apistol78/rv32/code/Runtime/GPIO.h

#pragma once

#include "Common.h"

// Directions
#define GPIO_INPUT	0
#define GPIO_OUTPUT	1

// Levels
#define GPIO_LOW	0
#define GPIO_HIGH	1

void gpio_set_direction(int pin, int direction);

void gpio_set_pin(int pin, int level);
