apistol78/rv32/board/terasic_cv_gx/ip/IP_SDRAM/alt_mem_ddrx_ecc_encoder_32_syn.v

// (C) 2001-2021 Intel Corporation. All rights reserved.
// Your use of Intel Corporation's design tools, logic functions and other 
// software and tools, and its AMPP partner logic functions, and any output 
// files from any of the foregoing (including device programming or simulation 
// files), and any associated documentation or information are expressly subject 
// to the terms and conditions of the Intel Program License Subscription 
// Agreement, Intel FPGA IP License Agreement, or other applicable 
// license agreement, including, without limitation, that your use is for the 
// sole purpose of programming logic devices manufactured by Intel and sold by 
// Intel or its authorized distributors.  Please refer to the applicable 
// agreement for further details.


// megafunction wizard: %ALTECC%
// GENERATION: STANDARD
// VERSION: WM1.0
// MODULE: altecc_encoder 

// ============================================================
// File Name: alt_mem_ddrx_ecc_encoder_32.v
// Megafunction Name(s):
// 			altecc_encoder
//
// Simulation Library Files(s):
// 			
// ============================================================
// ************************************************************
// THIS IS A WIZARD-GENERATED FILE. DO NOT EDIT THIS FILE!
//
// 10.0 Internal Build 257 07/26/2010 SP 1 PN Full Version
// ************************************************************


//Copyright (C) 1991-2010 Altera Corporation
//Your use of Altera Corporation's design tools, logic functions 
//and other software and tools, and its AMPP partner logic 
//functions, and any output files from any of the foregoing 
//(including device programming or simulation files), and any 
//associated documentation or information are expressly subject 
//to the terms and conditions of the Altera Program License 
//Subscription Agreement, Altera MegaCore Function License 
//Agreement, or other applicable license agreement, including, 
//without limitation, that your use is for the sole purpose of 
//programming logic devices manufactured by Altera and sold by 
//Altera or its authorized distributors.  Please refer to the 
//applicable agreement for further details.


//altecc_encoder device_family="Stratix III" lpm_pipeline=0 width_codeword=39 width_dataword=32 data q
//VERSION_BEGIN 10.0SP1 cbx_altecc_encoder 2010:07:26:21:21:15:PN cbx_mgl 2010:07:26:21:25:47:PN  VERSION_END
// synthesis VERILOG_INPUT_VERSION VERILOG_2001
// altera message_off 10463


//synthesis_resources = 
//synopsys translate_off
`timescale 1 ps / 1 ps
//synopsys translate_on
module  alt_mem_ddrx_ecc_encoder_32_altecc_encoder #
    ( parameter
        CFG_ECC_ENC_REG = 0
    )
	( 
        clk,
        reset_n,
	    data,
	    q
    ) /* synthesis synthesis_clearbox=1 */;
    input           clk;
    input           reset_n;
	input   [31:0]  data;
	output   [38:0]  q;

	wire  [31:0]  data_wire;
	wire  [17:0]  parity_01_wire;
	wire  [9:0]  parity_02_wire;
	wire  [4:0]  parity_03_wire;
	wire  [1:0]  parity_04_wire;
	wire  [0:0]  parity_05_wire;
	wire  [5:0]  parity_06_wire;
    wire  [37:0]  parity_final;
	wire  [37:0]  parity_final_wire;
    reg   [37:0]  parity_final_reg;
	wire  [37:0]  q_wire;
    reg   [37:0]  q_reg;

	assign
		data_wire = data,
		parity_01_wire = {
                            (data_wire[30] ^ parity_01_wire[16]),
                            (data_wire[28] ^ parity_01_wire[15]),
                            (data_wire[26] ^ parity_01_wire[14]),
                            (data_wire[25] ^ parity_01_wire[13]),
                            (data_wire[23] ^ parity_01_wire[12]),
                            (data_wire[21] ^ parity_01_wire[11]),
                            (data_wire[19] ^ parity_01_wire[10]),
                            (data_wire[17] ^ parity_01_wire[9]),
                            (data_wire[15] ^ parity_01_wire[8]),
                            (data_wire[13] ^ parity_01_wire[7]),
                            (data_wire[11] ^ parity_01_wire[6]),
                            (data_wire[10] ^ parity_01_wire[5]),
                            (data_wire[8] ^ parity_01_wire[4]),
                            (data_wire[6] ^ parity_01_wire[3]),
                            (data_wire[4] ^ parity_01_wire[2]),
                            (data_wire[3] ^ parity_01_wire[1]),
                            (data_wire[1] ^ parity_01_wire[0]),
                            data_wire[0]
                         },
		parity_02_wire = {
                            (data_wire[31] ^ parity_02_wire[8]),
                            ((data_wire[27] ^ data_wire[28]) ^ parity_02_wire[7]),
                            ((data_wire[24] ^ data_wire[25]) ^ parity_02_wire[6]),
                            ((data_wire[20] ^ data_wire[21]) ^ parity_02_wire[5]),
                            ((data_wire[16] ^ data_wire[17]) ^ parity_02_wire[4]),
                            ((data_wire[12] ^ data_wire[13]) ^ parity_02_wire[3]),
                            ((data_wire[9] ^ data_wire[10]) ^ parity_02_wire[2]),
                            ((data_wire[5] ^ data_wire[6]) ^ parity_02_wire[1]),
                            ((data_wire[2] ^ data_wire[3]) ^ parity_02_wire[0]),
                            data_wire[0]
                         },
		parity_03_wire = {
                            (((data_wire[29] ^ data_wire[30]) ^ data_wire[31]) ^ parity_03_wire[3]),
                            ((((data_wire[22] ^ data_wire[23]) ^ data_wire[24]) ^ data_wire[25]) ^ parity_03_wire[2]),
                            ((((data_wire[14] ^ data_wire[15]) ^ data_wire[16]) ^ data_wire[17]) ^ parity_03_wire[1]),
                            ((((data_wire[7] ^ data_wire[8]) ^ data_wire[9]) ^ data_wire[10]) ^ parity_03_wire[0]),
                            ((data_wire[1] ^ data_wire[2]) ^ data_wire[3])
                         },
		parity_04_wire = {
                            ((((((((data_wire[18] ^ data_wire[19]) ^ data_wire[20]) ^ data_wire[21]) ^ data_wire[22]) ^ data_wire[23]) ^ data_wire[24]) ^ data_wire[25]) ^ parity_04_wire[0]),
                            ((((((data_wire[4] ^ data_wire[5]) ^ data_wire[6]) ^ data_wire[7]) ^ data_wire[8]) ^ data_wire[9]) ^ data_wire[10])
                         },
		parity_05_wire = {
                            ((((((((((((((data_wire[11] ^ data_wire[12]) ^ data_wire[13]) ^ data_wire[14]) ^ data_wire[15]) ^ data_wire[16]) ^ data_wire[17]) ^ data_wire[18]) ^ data_wire[19]) ^ data_wire[20]) ^ data_wire[21]) ^ data_wire[22]) ^ data_wire[23]) ^ data_wire[24]) ^ data_wire[25])
                         },
		parity_06_wire = {
                            (data_wire[31] ^ parity_06_wire[4]),
                            (data_wire[30] ^ parity_06_wire[3]),
                            (data_wire[29] ^ parity_06_wire[2]),
                            (data_wire[28] ^ parity_06_wire[1]),
                            (data_wire[27] ^ parity_06_wire[0]),
                            data_wire[26]
                         },
		parity_final_wire = {
                                (q_wire[37] ^ parity_final_wire[36]),
                                (q_wire[36] ^ parity_final_wire[35]),
                                (q_wire[35] ^ parity_final_wire[34]),
                                (q_wire[34] ^ parity_final_wire[33]),
                                (q_wire[33] ^ parity_final_wire[32]),
                                (q_wire[32] ^ parity_final_wire[31]),
                                (q_wire[31] ^ parity_final_wire[30]),
                                (q_wire[30] ^ parity_final_wire[29]),
                                (q_wire[29] ^ parity_final_wire[28]),
                                (q_wire[28] ^ parity_final_wire[27]),
                                (q_wire[27] ^ parity_final_wire[26]),
                                (q_wire[26] ^ parity_final_wire[25]),
                                (q_wire[25] ^ parity_final_wire[24]),
                                (q_wire[24] ^ parity_final_wire[23]),
                                (q_wire[23] ^ parity_final_wire[22]),
                                (q_wire[22] ^ parity_final_wire[21]),
                                (q_wire[21] ^ parity_final_wire[20]),
                                (q_wire[20] ^ parity_final_wire[19]),
                                (q_wire[19] ^ parity_final_wire[18]),
                                (q_wire[18] ^ parity_final_wire[17]),
                                (q_wire[17] ^ parity_final_wire[16]),
                                (q_wire[16] ^ parity_final_wire[15]),
                                (q_wire[15] ^ parity_final_wire[14]),
                                (q_wire[14] ^ parity_final_wire[13]),
                                (q_wire[13] ^ parity_final_wire[12]),
                                (q_wire[12] ^ parity_final_wire[11]),
                                (q_wire[11] ^ parity_final_wire[10]),
                                (q_wire[10] ^ parity_final_wire[9]),
                                (q_wire[9] ^ parity_final_wire[8]),
                                (q_wire[8] ^ parity_final_wire[7]),
                                (q_wire[7] ^ parity_final_wire[6]),
                                (q_wire[6] ^ parity_final_wire[5]),
                                (q_wire[5] ^ parity_final_wire[4]),
                                (q_wire[4] ^ parity_final_wire[3]),
                                (q_wire[3] ^ parity_final_wire[2]),
                                (q_wire[2] ^ parity_final_wire[1]),
                                (q_wire[1] ^ parity_final_wire[0]),
                                 q_wire[0]
                            },
        parity_final = {
                            (q_reg[37] ^ parity_final[36]),
                            (q_reg[36] ^ parity_final[35]),
                            (q_reg[35] ^ parity_final[34]),
                            (q_reg[34] ^ parity_final[33]),
                            (q_reg[33] ^ parity_final[32]),
                            (q_reg[32] ^ parity_final[31]),
                            parity_final_reg[31 : 0]
                       },
        q = {parity_final[37], q_reg},
		q_wire = {parity_06_wire[5], parity_05_wire[0], parity_04_wire[1], parity_03_wire[4], parity_02_wire[9], parity_01_wire[17], data_wire};
        
        generate
            if (CFG_ECC_ENC_REG)
            begin
                always @ (posedge clk or negedge reset_n)
                begin
                    if (!reset_n)
                    begin
                        q_reg            <= 0;
                        parity_final_reg <= 0;
                    end
                    else
                    begin
                        q_reg            <= q_wire;
                        parity_final_reg <= parity_final_wire;
                    end
                end
            end
            else
            begin
                always @ (*)
                begin
                    q_reg            = q_wire;
                    parity_final_reg = parity_final_wire;
                end
            end
        endgenerate
        
endmodule //alt_mem_ddrx_ecc_encoder_32_altecc_encoder
//VALID FILE


// synopsys translate_off
`timescale 1 ps / 1 ps
// synopsys translate_on
module alt_mem_ddrx_ecc_encoder_32 #
    ( parameter
        CFG_ECC_ENC_REG = 0
    )
    (
        clk,
        reset_n,
	    data,
	    q
    )/* synthesis synthesis_clearbox = 1 */;

    input           clk;
    input           reset_n;
	input	[31:0]  data;
	output	[38:0]  q;

	wire [38:0] sub_wire0;
	wire [38:0] q = sub_wire0[38:0];

	alt_mem_ddrx_ecc_encoder_32_altecc_encoder #
        (
            .CFG_ECC_ENC_REG (CFG_ECC_ENC_REG)
        )
    alt_mem_ddrx_ecc_encoder_32_altecc_encoder_component
        (
            .clk (clk),
            .reset_n (reset_n),
		    .data (data),
		    .q (sub_wire0)
        );

endmodule

// ============================================================
// CNX file retrieval info
// ============================================================
// Retrieval info: PRIVATE: INTENDED_DEVICE_FAMILY STRING "Stratix III"
// Retrieval info: PRIVATE: SYNTH_WRAPPER_GEN_POSTFIX STRING "1"
// Retrieval info: LIBRARY: altera_mf altera_mf.altera_mf_components.all
// Retrieval info: CONSTANT: INTENDED_DEVICE_FAMILY STRING "Stratix III"
// Retrieval info: CONSTANT: lpm_pipeline NUMERIC "0"
// Retrieval info: CONSTANT: width_codeword NUMERIC "39"
// Retrieval info: CONSTANT: width_dataword NUMERIC "32"
// Retrieval info: USED_PORT: data 0 0 32 0 INPUT NODEFVAL "data[31..0]"
// Retrieval info: USED_PORT: q 0 0 39 0 OUTPUT NODEFVAL "q[38..0]"
// Retrieval info: CONNECT: @data 0 0 32 0 data 0 0 32 0
// Retrieval info: CONNECT: q 0 0 39 0 @q 0 0 39 0
// Retrieval info: GEN_FILE: TYPE_NORMAL alt_mem_ddrx_ecc_encoder.v FALSE
// Retrieval info: GEN_FILE: TYPE_NORMAL alt_mem_ddrx_ecc_encoder.inc FALSE
// Retrieval info: GEN_FILE: TYPE_NORMAL alt_mem_ddrx_ecc_encoder.cmp FALSE
// Retrieval info: GEN_FILE: TYPE_NORMAL alt_mem_ddrx_ecc_encoder.bsf FALSE
// Retrieval info: GEN_FILE: TYPE_NORMAL alt_mem_ddrx_ecc_encoder_inst.v FALSE
// Retrieval info: GEN_FILE: TYPE_NORMAL alt_mem_ddrx_ecc_encoder_bb.v FALSE
// Retrieval info: GEN_FILE: TYPE_NORMAL alt_mem_ddrx_ecc_encoder_32.v TRUE
// Retrieval info: GEN_FILE: TYPE_NORMAL alt_mem_ddrx_ecc_encoder_32.inc FALSE
// Retrieval info: GEN_FILE: TYPE_NORMAL alt_mem_ddrx_ecc_encoder_32.cmp FALSE
// Retrieval info: GEN_FILE: TYPE_NORMAL alt_mem_ddrx_ecc_encoder_32.bsf FALSE
// Retrieval info: GEN_FILE: TYPE_NORMAL alt_mem_ddrx_ecc_encoder_32_inst.v FALSE
// Retrieval info: GEN_FILE: TYPE_NORMAL alt_mem_ddrx_ecc_encoder_32_bb.v FALSE
// Retrieval info: GEN_FILE: TYPE_NORMAL alt_mem_ddrx_ecc_encoder_32_syn.v TRUE
