apistol78/rv32/board/terasic_cv_gx/SoC.qsf

# -------------------------------------------------------------------------- #
#
# Copyright (C) 2021  Intel Corporation. All rights reserved.
# Your use of Intel Corporation's design tools, logic functions 
# and other software and tools, and any partner logic 
# functions, and any output files from any of the foregoing 
# (including device programming or simulation files), and any 
# associated documentation or information are expressly subject 
# to the terms and conditions of the Intel Program License 
# Subscription Agreement, the Intel Quartus Prime License Agreement,
# the Intel FPGA IP License Agreement, or other applicable license
# agreement, including, without limitation, that your use is for
# the sole purpose of programming logic devices manufactured by
# Intel and sold by Intel or its authorized distributors.  Please
# refer to the applicable agreement for further details, at
# https://fpgasoftware.intel.com/eula.
#
# -------------------------------------------------------------------------- #
#
# Quartus Prime
# Version 21.1.0 Build 842 10/21/2021 SJ Lite Edition
# Date created = 17:36:14  December 13, 2021
#
# -------------------------------------------------------------------------- #
#
# Notes:
#
# 1) The default values for assignments are stored in the file:
#		MyTest_assignment_defaults.qdf
#    If this file doesn't exist, see file:
#		assignment_defaults.qdf
#
# 2) Intel recommends that you do not modify this file. This
#    file is updated automatically by the Quartus Prime software
#    and any changes you make may be lost or overwritten.
#
# -------------------------------------------------------------------------- #


set_global_assignment -name FAMILY "Cyclone V"
set_global_assignment -name DEVICE 5CGXFC5C6F27C7
set_global_assignment -name TOP_LEVEL_ENTITY SoC
set_global_assignment -name ORIGINAL_QUARTUS_VERSION 12
set_global_assignment -name PROJECT_CREATION_TIME_DATE "TUE JUN  4 20:41:15 2013"
set_global_assignment -name LAST_QUARTUS_VERSION "21.1.0 Lite Edition"
set_global_assignment -name PROJECT_OUTPUT_DIRECTORY output_files
set_global_assignment -name DEVICE_FILTER_PACKAGE FBGA
set_global_assignment -name CYCLONEII_RESERVE_NCEO_AFTER_CONFIGURATION "USE AS REGULAR IO"
set_location_assignment PIN_AB22 -to ADC_CONVST
set_location_assignment PIN_AA21 -to ADC_SCK
set_location_assignment PIN_Y10 -to ADC_SDI
set_location_assignment PIN_W10 -to ADC_SDO
set_location_assignment PIN_D7 -to AUD_ADCDAT
set_location_assignment PIN_C7 -to AUD_ADCLRCK
set_location_assignment PIN_E6 -to AUD_BCLK
set_location_assignment PIN_H10 -to AUD_DACDAT
set_location_assignment PIN_G10 -to AUD_DACLRCK
set_location_assignment PIN_D6 -to AUD_XCK
set_location_assignment PIN_U12 -to CLOCK_125_p
set_location_assignment PIN_R20 -to CLOCK_50_B5B
set_location_assignment PIN_N20 -to CLOCK_50_B6A
set_location_assignment PIN_H12 -to CLOCK_50_B7A
set_location_assignment PIN_M10 -to CLOCK_50_B8A
set_location_assignment PIN_AB24 -to CPU_RESET_n
set_location_assignment PIN_AE6 -to DDR2LP_CA[0]
set_location_assignment PIN_AF6 -to DDR2LP_CA[1]
set_location_assignment PIN_AF7 -to DDR2LP_CA[2]
set_location_assignment PIN_AF8 -to DDR2LP_CA[3]
set_location_assignment PIN_U10 -to DDR2LP_CA[4]
set_location_assignment PIN_U11 -to DDR2LP_CA[5]
set_location_assignment PIN_AE9 -to DDR2LP_CA[6]
set_location_assignment PIN_AF9 -to DDR2LP_CA[7]
set_location_assignment PIN_AB12 -to DDR2LP_CA[8]
set_location_assignment PIN_AB11 -to DDR2LP_CA[9]
set_location_assignment PIN_AF14 -to DDR2LP_CKE[0]
set_location_assignment PIN_AE13 -to DDR2LP_CKE[1]
set_location_assignment PIN_P10 -to DDR2LP_CK_n
set_location_assignment PIN_N10 -to DDR2LP_CK_p
set_location_assignment PIN_R11 -to DDR2LP_CS_n[0]
set_location_assignment PIN_T11 -to DDR2LP_CS_n[1]
set_location_assignment PIN_AF11 -to DDR2LP_DM[0]
set_location_assignment PIN_AE18 -to DDR2LP_DM[1]
set_location_assignment PIN_AE20 -to DDR2LP_DM[2]
set_location_assignment PIN_AE24 -to DDR2LP_DM[3]
set_location_assignment PIN_AA14 -to DDR2LP_DQ[0]
set_location_assignment PIN_Y14 -to DDR2LP_DQ[1]
set_location_assignment PIN_AD11 -to DDR2LP_DQ[2]
set_location_assignment PIN_AD12 -to DDR2LP_DQ[3]
set_location_assignment PIN_Y13 -to DDR2LP_DQ[4]
set_location_assignment PIN_W12 -to DDR2LP_DQ[5]
set_location_assignment PIN_AD10 -to DDR2LP_DQ[6]
set_location_assignment PIN_AF12 -to DDR2LP_DQ[7]
set_location_assignment PIN_AC15 -to DDR2LP_DQ[8]
set_location_assignment PIN_AB15 -to DDR2LP_DQ[9]
set_location_assignment PIN_AC14 -to DDR2LP_DQ[10]
set_location_assignment PIN_AF13 -to DDR2LP_DQ[11]
set_location_assignment PIN_AB16 -to DDR2LP_DQ[12]
set_location_assignment PIN_AA16 -to DDR2LP_DQ[13]
set_location_assignment PIN_AE14 -to DDR2LP_DQ[14]
set_location_assignment PIN_AF18 -to DDR2LP_DQ[15]
set_location_assignment PIN_AD16 -to DDR2LP_DQ[16]
set_location_assignment PIN_AD17 -to DDR2LP_DQ[17]
set_location_assignment PIN_AC18 -to DDR2LP_DQ[18]
set_location_assignment PIN_AF19 -to DDR2LP_DQ[19]
set_location_assignment PIN_AC17 -to DDR2LP_DQ[20]
set_location_assignment PIN_AB17 -to DDR2LP_DQ[21]
set_location_assignment PIN_AF21 -to DDR2LP_DQ[22]
set_location_assignment PIN_AE21 -to DDR2LP_DQ[23]
set_location_assignment PIN_AE15 -to DDR2LP_DQ[24]
set_location_assignment PIN_AE16 -to DDR2LP_DQ[25]
set_location_assignment PIN_AC20 -to DDR2LP_DQ[26]
set_location_assignment PIN_AD21 -to DDR2LP_DQ[27]
set_location_assignment PIN_AF16 -to DDR2LP_DQ[28]
set_location_assignment PIN_AF17 -to DDR2LP_DQ[29]
set_location_assignment PIN_AD23 -to DDR2LP_DQ[30]
set_location_assignment PIN_AF23 -to DDR2LP_DQ[31]
set_location_assignment PIN_W13 -to DDR2LP_DQS_n[0]
set_location_assignment PIN_V14 -to DDR2LP_DQS_n[1]
set_location_assignment PIN_W15 -to DDR2LP_DQS_n[2]
set_location_assignment PIN_W17 -to DDR2LP_DQS_n[3]
set_location_assignment PIN_V13 -to DDR2LP_DQS_p[0]
set_location_assignment PIN_U14 -to DDR2LP_DQS_p[1]
set_location_assignment PIN_V15 -to DDR2LP_DQS_p[2]
set_location_assignment PIN_W16 -to DDR2LP_DQS_p[3]
set_location_assignment PIN_AE11 -to DDR2LP_OCT_RZQ
set_location_assignment PIN_Y25 -to HDMI_TX_CLK
set_location_assignment PIN_V23 -to HDMI_TX_D[0]
set_location_assignment PIN_AA26 -to HDMI_TX_D[1]
set_location_assignment PIN_W25 -to HDMI_TX_D[2]
set_location_assignment PIN_W26 -to HDMI_TX_D[3]
set_location_assignment PIN_V24 -to HDMI_TX_D[4]
set_location_assignment PIN_V25 -to HDMI_TX_D[5]
set_location_assignment PIN_U24 -to HDMI_TX_D[6]
set_location_assignment PIN_T23 -to HDMI_TX_D[7]
set_location_assignment PIN_T24 -to HDMI_TX_D[8]
set_location_assignment PIN_T26 -to HDMI_TX_D[9]
set_location_assignment PIN_R23 -to HDMI_TX_D[10]
set_location_assignment PIN_R25 -to HDMI_TX_D[11]
set_location_assignment PIN_P22 -to HDMI_TX_D[12]
set_location_assignment PIN_P23 -to HDMI_TX_D[13]
set_location_assignment PIN_N25 -to HDMI_TX_D[14]
set_location_assignment PIN_P26 -to HDMI_TX_D[15]
set_location_assignment PIN_P21 -to HDMI_TX_D[16]
set_location_assignment PIN_R24 -to HDMI_TX_D[17]
set_location_assignment PIN_R26 -to HDMI_TX_D[18]
set_location_assignment PIN_AB26 -to HDMI_TX_D[19]
set_location_assignment PIN_AA24 -to HDMI_TX_D[20]
set_location_assignment PIN_AB25 -to HDMI_TX_D[21]
set_location_assignment PIN_AC25 -to HDMI_TX_D[22]
set_location_assignment PIN_AD25 -to HDMI_TX_D[23]
set_location_assignment PIN_Y26 -to HDMI_TX_DE
set_location_assignment PIN_U26 -to HDMI_TX_HS
set_location_assignment PIN_T12 -to HDMI_TX_INT
set_location_assignment PIN_U25 -to HDMI_TX_VS
set_location_assignment PIN_V19 -to HEX0[0]
set_location_assignment PIN_V18 -to HEX0[1]
set_location_assignment PIN_V17 -to HEX0[2]
set_location_assignment PIN_W18 -to HEX0[3]
set_location_assignment PIN_Y20 -to HEX0[4]
set_location_assignment PIN_Y19 -to HEX0[5]
set_location_assignment PIN_Y18 -to HEX0[6]
set_location_assignment PIN_AA18 -to HEX1[0]
set_location_assignment PIN_AD26 -to HEX1[1]
set_location_assignment PIN_AB19 -to HEX1[2]
set_location_assignment PIN_AE26 -to HEX1[3]
set_location_assignment PIN_AE25 -to HEX1[4]
set_location_assignment PIN_AC19 -to HEX1[5]
set_location_assignment PIN_AF24 -to HEX1[6]
set_location_assignment PIN_N9 -to HSMC_CLKIN0
set_location_assignment PIN_G14 -to HSMC_CLKIN_n[1]
set_location_assignment PIN_K9 -to HSMC_CLKIN_n[2]
set_location_assignment PIN_G15 -to HSMC_CLKIN_p[1]
set_location_assignment PIN_L8 -to HSMC_CLKIN_p[2]
set_location_assignment PIN_A7 -to HSMC_CLKOUT0
set_location_assignment PIN_A18 -to HSMC_CLKOUT_n[1]
set_location_assignment PIN_A16 -to HSMC_CLKOUT_n[2]
set_location_assignment PIN_A19 -to HSMC_CLKOUT_p[1]
set_location_assignment PIN_A17 -to HSMC_CLKOUT_p[2]
set_location_assignment PIN_D11 -to HSMC_D[0]
set_location_assignment PIN_H14 -to HSMC_D[1]
set_location_assignment PIN_D12 -to HSMC_D[2]
set_location_assignment PIN_H13 -to HSMC_D[3]
set_location_assignment PIN_AD2 -to HSMC_GXB_RX_p[0]
set_location_assignment PIN_AB2 -to HSMC_GXB_RX_p[1]
set_location_assignment PIN_Y2 -to HSMC_GXB_RX_p[2]
set_location_assignment PIN_V2 -to HSMC_GXB_RX_p[3]
set_location_assignment PIN_AE4 -to HSMC_GXB_TX_p[0]
set_location_assignment PIN_AC4 -to HSMC_GXB_TX_p[1]
set_location_assignment PIN_AA4 -to HSMC_GXB_TX_p[2]
set_location_assignment PIN_W4 -to HSMC_GXB_TX_p[3]
set_location_assignment PIN_M12 -to HSMC_RX_n[0]
set_location_assignment PIN_L11 -to HSMC_RX_n[1]
set_location_assignment PIN_H17 -to HSMC_RX_n[2]
set_location_assignment PIN_K11 -to HSMC_RX_n[3]
set_location_assignment PIN_J16 -to HSMC_RX_n[4]
set_location_assignment PIN_J11 -to HSMC_RX_n[5]
set_location_assignment PIN_G17 -to HSMC_RX_n[6]
set_location_assignment PIN_F12 -to HSMC_RX_n[7]
set_location_assignment PIN_F18 -to HSMC_RX_n[8]
set_location_assignment PIN_E15 -to HSMC_RX_n[9]
set_location_assignment PIN_D13 -to HSMC_RX_n[10]
set_location_assignment PIN_D15 -to HSMC_RX_n[11]
set_location_assignment PIN_D16 -to HSMC_RX_n[12]
set_location_assignment PIN_D17 -to HSMC_RX_n[13]
set_location_assignment PIN_E19 -to HSMC_RX_n[14]
set_location_assignment PIN_D20 -to HSMC_RX_n[15]
set_location_assignment PIN_A24 -to HSMC_RX_n[16]
set_location_assignment PIN_N12 -to HSMC_RX_p[0]
set_location_assignment PIN_M11 -to HSMC_RX_p[1]
set_location_assignment PIN_H18 -to HSMC_RX_p[2]
set_location_assignment PIN_L12 -to HSMC_RX_p[3]
set_location_assignment PIN_H15 -to HSMC_RX_p[4]
set_location_assignment PIN_J12 -to HSMC_RX_p[5]
set_location_assignment PIN_G16 -to HSMC_RX_p[6]
set_location_assignment PIN_G12 -to HSMC_RX_p[7]
set_location_assignment PIN_E18 -to HSMC_RX_p[8]
set_location_assignment PIN_F16 -to HSMC_RX_p[9]
set_location_assignment PIN_E13 -to HSMC_RX_p[10]
set_location_assignment PIN_C14 -to HSMC_RX_p[11]
set_location_assignment PIN_E16 -to HSMC_RX_p[12]
set_location_assignment PIN_D18 -to HSMC_RX_p[13]
set_location_assignment PIN_E20 -to HSMC_RX_p[14]
set_location_assignment PIN_D21 -to HSMC_RX_p[15]
set_location_assignment PIN_B24 -to HSMC_RX_p[16]
set_location_assignment PIN_E11 -to HSMC_TX_n[0]
set_location_assignment PIN_B9 -to HSMC_TX_n[1]
set_location_assignment PIN_C10 -to HSMC_TX_n[2]
set_location_assignment PIN_B11 -to HSMC_TX_n[3]
set_location_assignment PIN_A11 -to HSMC_TX_n[4]
set_location_assignment PIN_B19 -to HSMC_TX_n[5]
set_location_assignment PIN_C15 -to HSMC_TX_n[6]
set_location_assignment PIN_A21 -to HSMC_TX_n[7]
set_location_assignment PIN_C12 -to HSMC_TX_n[8]
set_location_assignment PIN_A9 -to HSMC_TX_n[9]
set_location_assignment PIN_A13 -to HSMC_TX_n[10]
set_location_assignment PIN_C22 -to HSMC_TX_n[11]
set_location_assignment PIN_B14 -to HSMC_TX_n[12]
set_location_assignment PIN_A22 -to HSMC_TX_n[13]
set_location_assignment PIN_B17 -to HSMC_TX_n[14]
set_location_assignment PIN_C18 -to HSMC_TX_n[15]
set_location_assignment PIN_B20 -to HSMC_TX_n[16]
set_location_assignment PIN_E10 -to HSMC_TX_p[0]
set_location_assignment PIN_C9 -to HSMC_TX_p[1]
set_location_assignment PIN_D10 -to HSMC_TX_p[2]
set_location_assignment PIN_A12 -to HSMC_TX_p[3]
set_location_assignment PIN_B10 -to HSMC_TX_p[4]
set_location_assignment PIN_C20 -to HSMC_TX_p[5]
set_location_assignment PIN_B15 -to HSMC_TX_p[6]
set_location_assignment PIN_B22 -to HSMC_TX_p[7]
set_location_assignment PIN_C13 -to HSMC_TX_p[8]
set_location_assignment PIN_A8 -to HSMC_TX_p[9]
set_location_assignment PIN_B12 -to HSMC_TX_p[10]
set_location_assignment PIN_C23 -to HSMC_TX_p[11]
set_location_assignment PIN_A14 -to HSMC_TX_p[12]
set_location_assignment PIN_A23 -to HSMC_TX_p[13]
set_location_assignment PIN_C17 -to HSMC_TX_p[14]
set_location_assignment PIN_C19 -to HSMC_TX_p[15]
set_location_assignment PIN_B21 -to HSMC_TX_p[16]
set_location_assignment PIN_B7 -to I2C_SCL
set_location_assignment PIN_G11 -to I2C_SDA
set_location_assignment PIN_P11 -to KEY[0]
set_location_assignment PIN_P12 -to KEY[1]
set_location_assignment PIN_Y15 -to KEY[2]
set_location_assignment PIN_Y16 -to KEY[3]
set_location_assignment PIN_L7 -to LEDG[0]
set_location_assignment PIN_K6 -to LEDG[1]
set_location_assignment PIN_D8 -to LEDG[2]
set_location_assignment PIN_E9 -to LEDG[3]
set_location_assignment PIN_A5 -to LEDG[4]
set_location_assignment PIN_B6 -to LEDG[5]
set_location_assignment PIN_H8 -to LEDG[6]
set_location_assignment PIN_H9 -to LEDG[7]
set_location_assignment PIN_F7 -to LEDR[0]
set_location_assignment PIN_F6 -to LEDR[1]
set_location_assignment PIN_G6 -to LEDR[2]
set_location_assignment PIN_G7 -to LEDR[3]
set_location_assignment PIN_J8 -to LEDR[4]
set_location_assignment PIN_J7 -to LEDR[5]
set_location_assignment PIN_K10 -to LEDR[6]
set_location_assignment PIN_K8 -to LEDR[7]
set_location_assignment PIN_H7 -to LEDR[8]
set_location_assignment PIN_J10 -to LEDR[9]
set_location_assignment PIN_V6 -to REFCLK_p0
set_location_assignment PIN_N7 -to REFCLK_p1
set_location_assignment PIN_AB6 -to SD_CLK
set_location_assignment PIN_W8 -to SD_CMD
set_location_assignment PIN_U7 -to SD_DAT[0]
set_location_assignment PIN_T7 -to SD_DAT[1]
set_location_assignment PIN_V8 -to SD_DAT[2]
set_location_assignment PIN_T8 -to SD_DAT[3]
set_location_assignment PIN_M2 -to SMA_GXB_RX_p
set_location_assignment PIN_K2 -to SMA_GXB_TX_p
set_location_assignment PIN_B25 -to SRAM_A[0]
set_location_assignment PIN_B26 -to SRAM_A[1]
set_location_assignment PIN_H19 -to SRAM_A[2]
set_location_assignment PIN_H20 -to SRAM_A[3]
set_location_assignment PIN_D25 -to SRAM_A[4]
set_location_assignment PIN_C25 -to SRAM_A[5]
set_location_assignment PIN_J20 -to SRAM_A[6]
set_location_assignment PIN_J21 -to SRAM_A[7]
set_location_assignment PIN_D22 -to SRAM_A[8]
set_location_assignment PIN_E23 -to SRAM_A[9]
set_location_assignment PIN_G20 -to SRAM_A[10]
set_location_assignment PIN_F21 -to SRAM_A[11]
set_location_assignment PIN_E21 -to SRAM_A[12]
set_location_assignment PIN_F22 -to SRAM_A[13]
set_location_assignment PIN_J25 -to SRAM_A[14]
set_location_assignment PIN_J26 -to SRAM_A[15]
set_location_assignment PIN_N24 -to SRAM_A[16]
set_location_assignment PIN_M24 -to SRAM_A[17]
set_location_assignment PIN_N23 -to SRAM_CE_n
set_location_assignment PIN_E24 -to SRAM_D[0]
set_location_assignment PIN_E25 -to SRAM_D[1]
set_location_assignment PIN_K24 -to SRAM_D[2]
set_location_assignment PIN_K23 -to SRAM_D[3]
set_location_assignment PIN_F24 -to SRAM_D[4]
set_location_assignment PIN_G24 -to SRAM_D[5]
set_location_assignment PIN_L23 -to SRAM_D[6]
set_location_assignment PIN_L24 -to SRAM_D[7]
set_location_assignment PIN_H23 -to SRAM_D[8]
set_location_assignment PIN_H24 -to SRAM_D[9]
set_location_assignment PIN_H22 -to SRAM_D[10]
set_location_assignment PIN_J23 -to SRAM_D[11]
set_location_assignment PIN_F23 -to SRAM_D[12]
set_location_assignment PIN_G22 -to SRAM_D[13]
set_location_assignment PIN_L22 -to SRAM_D[14]
set_location_assignment PIN_K21 -to SRAM_D[15]
set_location_assignment PIN_H25 -to SRAM_LB_n
set_location_assignment PIN_M22 -to SRAM_OE_n
set_location_assignment PIN_M25 -to SRAM_UB_n
set_location_assignment PIN_G25 -to SRAM_WE_n
set_location_assignment PIN_AC9 -to SW[0]
set_location_assignment PIN_AE10 -to SW[1]
set_location_assignment PIN_AD13 -to SW[2]
set_location_assignment PIN_AC8 -to SW[3]
set_location_assignment PIN_W11 -to SW[4]
set_location_assignment PIN_AB10 -to SW[5]
set_location_assignment PIN_V10 -to SW[6]
set_location_assignment PIN_AC10 -to SW[7]
set_location_assignment PIN_Y11 -to SW[8]
set_location_assignment PIN_AE19 -to SW[9]
set_location_assignment PIN_M9 -to UART_RX
set_location_assignment PIN_L9 -to UART_TX
set_global_assignment -name STRATIX_DEVICE_IO_STANDARD "2.5 V"
set_global_assignment -name MIN_CORE_JUNCTION_TEMP 0
set_global_assignment -name MAX_CORE_JUNCTION_TEMP 85
set_global_assignment -name POWER_PRESET_COOLING_SOLUTION "23 MM HEAT SINK WITH 200 LFPM AIRFLOW"
set_global_assignment -name POWER_BOARD_THERMAL_MODEL "NONE (CONSERVATIVE)"
set_global_assignment -name OPTIMIZATION_TECHNIQUE BALANCED
set_global_assignment -name SYNTH_TIMING_DRIVEN_SYNTHESIS ON
set_global_assignment -name STRATIXV_CONFIGURATION_SCHEME "ACTIVE SERIAL X4"
set_global_assignment -name USE_CONFIGURATION_DEVICE ON
set_global_assignment -name STRATIXII_CONFIGURATION_DEVICE EPCQ256
set_global_assignment -name CRC_ERROR_OPEN_DRAIN ON
set_global_assignment -name OUTPUT_IO_TIMING_NEAR_END_VMEAS "HALF VCCIO" -rise
set_global_assignment -name OUTPUT_IO_TIMING_NEAR_END_VMEAS "HALF VCCIO" -fall
set_global_assignment -name OUTPUT_IO_TIMING_FAR_END_VMEAS "HALF SIGNAL SWING" -rise
set_global_assignment -name OUTPUT_IO_TIMING_FAR_END_VMEAS "HALF SIGNAL SWING" -fall
set_global_assignment -name ACTIVE_SERIAL_CLOCK FREQ_100MHZ
set_global_assignment -name OPTIMIZE_HOLD_TIMING "ALL PATHS"
set_global_assignment -name OPTIMIZE_MULTI_CORNER_TIMING ON
set_global_assignment -name FITTER_EFFORT "STANDARD FIT"
set_global_assignment -name BOARD "Cyclone V GX Starter Kit"
set_global_assignment -name PARTITION_NETLIST_TYPE SOURCE -section_id Top
set_global_assignment -name PARTITION_FITTER_PRESERVATION_LEVEL PLACEMENT_AND_ROUTING -section_id Top
set_global_assignment -name PARTITION_COLOR 16764057 -section_id Top
set_instance_assignment -name IO_STANDARD "1.2 V" -to ADC_CONVST
set_instance_assignment -name IO_STANDARD "1.2 V" -to ADC_SCK
set_instance_assignment -name IO_STANDARD "1.2 V" -to ADC_SDI
set_instance_assignment -name IO_STANDARD "1.2 V" -to ADC_SDO
set_instance_assignment -name IO_STANDARD "2.5 V" -to AUD_ADCDAT
set_instance_assignment -name IO_STANDARD "2.5 V" -to AUD_ADCLRCK
set_instance_assignment -name IO_STANDARD "2.5 V" -to AUD_BCLK
set_instance_assignment -name IO_STANDARD "2.5 V" -to AUD_DACDAT
set_instance_assignment -name IO_STANDARD "2.5 V" -to AUD_DACLRCK
set_instance_assignment -name IO_STANDARD "2.5 V" -to AUD_XCK
set_instance_assignment -name IO_STANDARD LVDS -to CLOCK_125_p
set_instance_assignment -name IO_STANDARD "3.3-V LVTTL" -to CLOCK_50_B5B
set_instance_assignment -name IO_STANDARD "3.3-V LVTTL" -to CLOCK_50_B6A
set_instance_assignment -name IO_STANDARD "2.5 V" -to CLOCK_50_B7A
set_instance_assignment -name IO_STANDARD "2.5 V" -to CLOCK_50_B8A
set_instance_assignment -name IO_STANDARD "3.3-V LVTTL" -to CPU_RESET_n
set_instance_assignment -name IO_STANDARD "1.2-V HSUL" -to DDR2LP_CA[0]
set_instance_assignment -name IO_STANDARD "1.2-V HSUL" -to DDR2LP_CA[1]
set_instance_assignment -name IO_STANDARD "1.2-V HSUL" -to DDR2LP_CA[2]
set_instance_assignment -name IO_STANDARD "1.2-V HSUL" -to DDR2LP_CA[3]
set_instance_assignment -name IO_STANDARD "1.2-V HSUL" -to DDR2LP_CA[4]
set_instance_assignment -name IO_STANDARD "1.2-V HSUL" -to DDR2LP_CA[5]
set_instance_assignment -name IO_STANDARD "1.2-V HSUL" -to DDR2LP_CA[6]
set_instance_assignment -name IO_STANDARD "1.2-V HSUL" -to DDR2LP_CA[7]
set_instance_assignment -name IO_STANDARD "1.2-V HSUL" -to DDR2LP_CA[8]
set_instance_assignment -name IO_STANDARD "1.2-V HSUL" -to DDR2LP_CA[9]
set_instance_assignment -name IO_STANDARD "1.2-V HSUL" -to DDR2LP_CKE[0]
set_instance_assignment -name IO_STANDARD "1.2-V HSUL" -to DDR2LP_CKE[1]
set_instance_assignment -name IO_STANDARD "DIFFERENTIAL 1.2-V HSUL" -to DDR2LP_CK_n
set_instance_assignment -name IO_STANDARD "DIFFERENTIAL 1.2-V HSUL" -to DDR2LP_CK_p
set_instance_assignment -name IO_STANDARD "1.2-V HSUL" -to DDR2LP_CS_n[0]
set_instance_assignment -name IO_STANDARD "1.2-V HSUL" -to DDR2LP_CS_n[1]
set_instance_assignment -name IO_STANDARD "1.2-V HSUL" -to DDR2LP_DM[0]
set_instance_assignment -name IO_STANDARD "1.2-V HSUL" -to DDR2LP_DM[1]
set_instance_assignment -name IO_STANDARD "1.2-V HSUL" -to DDR2LP_DM[2]
set_instance_assignment -name IO_STANDARD "1.2-V HSUL" -to DDR2LP_DM[3]
set_instance_assignment -name IO_STANDARD "1.2-V HSUL" -to DDR2LP_DQ[0]
set_instance_assignment -name IO_STANDARD "1.2-V HSUL" -to DDR2LP_DQ[1]
set_instance_assignment -name IO_STANDARD "1.2-V HSUL" -to DDR2LP_DQ[2]
set_instance_assignment -name IO_STANDARD "1.2-V HSUL" -to DDR2LP_DQ[3]
set_instance_assignment -name IO_STANDARD "1.2-V HSUL" -to DDR2LP_DQ[4]
set_instance_assignment -name IO_STANDARD "1.2-V HSUL" -to DDR2LP_DQ[5]
set_instance_assignment -name IO_STANDARD "1.2-V HSUL" -to DDR2LP_DQ[6]
set_instance_assignment -name IO_STANDARD "1.2-V HSUL" -to DDR2LP_DQ[7]
set_instance_assignment -name IO_STANDARD "1.2-V HSUL" -to DDR2LP_DQ[8]
set_instance_assignment -name IO_STANDARD "1.2-V HSUL" -to DDR2LP_DQ[9]
set_instance_assignment -name IO_STANDARD "1.2-V HSUL" -to DDR2LP_DQ[10]
set_instance_assignment -name IO_STANDARD "1.2-V HSUL" -to DDR2LP_DQ[11]
set_instance_assignment -name IO_STANDARD "1.2-V HSUL" -to DDR2LP_DQ[12]
set_instance_assignment -name IO_STANDARD "1.2-V HSUL" -to DDR2LP_DQ[13]
set_instance_assignment -name IO_STANDARD "1.2-V HSUL" -to DDR2LP_DQ[14]
set_instance_assignment -name IO_STANDARD "1.2-V HSUL" -to DDR2LP_DQ[15]
set_instance_assignment -name IO_STANDARD "1.2-V HSUL" -to DDR2LP_DQ[16]
set_instance_assignment -name IO_STANDARD "1.2-V HSUL" -to DDR2LP_DQ[17]
set_instance_assignment -name IO_STANDARD "1.2-V HSUL" -to DDR2LP_DQ[18]
set_instance_assignment -name IO_STANDARD "1.2-V HSUL" -to DDR2LP_DQ[19]
set_instance_assignment -name IO_STANDARD "1.2-V HSUL" -to DDR2LP_DQ[20]
set_instance_assignment -name IO_STANDARD "1.2-V HSUL" -to DDR2LP_DQ[21]
set_instance_assignment -name IO_STANDARD "1.2-V HSUL" -to DDR2LP_DQ[22]
set_instance_assignment -name IO_STANDARD "1.2-V HSUL" -to DDR2LP_DQ[23]
set_instance_assignment -name IO_STANDARD "1.2-V HSUL" -to DDR2LP_DQ[24]
set_instance_assignment -name IO_STANDARD "1.2-V HSUL" -to DDR2LP_DQ[25]
set_instance_assignment -name IO_STANDARD "1.2-V HSUL" -to DDR2LP_DQ[26]
set_instance_assignment -name IO_STANDARD "1.2-V HSUL" -to DDR2LP_DQ[27]
set_instance_assignment -name IO_STANDARD "1.2-V HSUL" -to DDR2LP_DQ[28]
set_instance_assignment -name IO_STANDARD "1.2-V HSUL" -to DDR2LP_DQ[29]
set_instance_assignment -name IO_STANDARD "1.2-V HSUL" -to DDR2LP_DQ[30]
set_instance_assignment -name IO_STANDARD "1.2-V HSUL" -to DDR2LP_DQ[31]
set_instance_assignment -name IO_STANDARD "DIFFERENTIAL 1.2-V HSUL" -to DDR2LP_DQS_n[0]
set_instance_assignment -name IO_STANDARD "DIFFERENTIAL 1.2-V HSUL" -to DDR2LP_DQS_n[1]
set_instance_assignment -name IO_STANDARD "DIFFERENTIAL 1.2-V HSUL" -to DDR2LP_DQS_n[2]
set_instance_assignment -name IO_STANDARD "DIFFERENTIAL 1.2-V HSUL" -to DDR2LP_DQS_n[3]
set_instance_assignment -name IO_STANDARD "DIFFERENTIAL 1.2-V HSUL" -to DDR2LP_DQS_p[0]
set_instance_assignment -name IO_STANDARD "DIFFERENTIAL 1.2-V HSUL" -to DDR2LP_DQS_p[1]
set_instance_assignment -name IO_STANDARD "DIFFERENTIAL 1.2-V HSUL" -to DDR2LP_DQS_p[2]
set_instance_assignment -name IO_STANDARD "DIFFERENTIAL 1.2-V HSUL" -to DDR2LP_DQS_p[3]
set_instance_assignment -name IO_STANDARD "1.2 V" -to DDR2LP_OCT_RZQ
set_instance_assignment -name IO_STANDARD "3.3-V LVTTL" -to HDMI_TX_CLK
set_instance_assignment -name IO_STANDARD "3.3-V LVTTL" -to HDMI_TX_D[0]
set_instance_assignment -name IO_STANDARD "3.3-V LVTTL" -to HDMI_TX_D[1]
set_instance_assignment -name IO_STANDARD "3.3-V LVTTL" -to HDMI_TX_D[2]
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
set_instance_assignment -name IO_STANDARD "2.5 V" -to LEDR[8]
set_instance_assignment -name IO_STANDARD "2.5 V" -to LEDR[9]
set_instance_assignment -name IO_STANDARD "1.5-V PCML" -to REFCLK_p0
set_instance_assignment -name IO_STANDARD "1.5-V PCML" -to REFCLK_p1
set_instance_assignment -name IO_STANDARD "3.3-V LVTTL" -to SD_CLK
set_instance_assignment -name IO_STANDARD "3.3-V LVTTL" -to SD_CMD
set_instance_assignment -name IO_STANDARD "3.3-V LVTTL" -to SD_DAT[0]
set_instance_assignment -name IO_STANDARD "3.3-V LVTTL" -to SD_DAT[1]
set_instance_assignment -name IO_STANDARD "3.3-V LVTTL" -to SD_DAT[2]
set_instance_assignment -name IO_STANDARD "3.3-V LVTTL" -to SD_DAT[3]
set_instance_assignment -name IO_STANDARD "1.5-V PCML" -to SMA_GXB_RX_p
set_instance_assignment -name IO_STANDARD "1.5-V PCML" -to SMA_GXB_TX_p
set_instance_assignment -name IO_STANDARD "3.3-V LVTTL" -to SRAM_A[0]
set_instance_assignment -name IO_STANDARD "3.3-V LVTTL" -to SRAM_A[1]
set_instance_assignment -name IO_STANDARD "3.3-V LVTTL" -to SRAM_A[2]
set_instance_assignment -name IO_STANDARD "3.3-V LVTTL" -to SRAM_A[3]
set_instance_assignment -name IO_STANDARD "3.3-V LVTTL" -to SRAM_A[4]
set_instance_assignment -name IO_STANDARD "3.3-V LVTTL" -to SRAM_A[5]
set_instance_assignment -name IO_STANDARD "3.3-V LVTTL" -to SRAM_A[6]
set_instance_assignment -name IO_STANDARD "3.3-V LVTTL" -to SRAM_A[7]
set_instance_assignment -name IO_STANDARD "3.3-V LVTTL" -to SRAM_A[8]
set_instance_assignment -name IO_STANDARD "3.3-V LVTTL" -to SRAM_A[9]
set_instance_assignment -name IO_STANDARD "3.3-V LVTTL" -to SRAM_A[10]
set_instance_assignment -name IO_STANDARD "3.3-V LVTTL" -to SRAM_A[11]
set_instance_assignment -name IO_STANDARD "3.3-V LVTTL" -to SRAM_A[12]
set_instance_assignment -name IO_STANDARD "3.3-V LVTTL" -to SRAM_A[13]
set_instance_assignment -name IO_STANDARD "3.3-V LVTTL" -to SRAM_A[14]
set_instance_assignment -name IO_STANDARD "3.3-V LVTTL" -to SRAM_A[15]
set_instance_assignment -name IO_STANDARD "3.3-V LVTTL" -to SRAM_A[16]
set_instance_assignment -name IO_STANDARD "3.3-V LVTTL" -to SRAM_A[17]
set_instance_assignment -name IO_STANDARD "3.3-V LVTTL" -to SRAM_CE_n
set_instance_assignment -name IO_STANDARD "3.3-V LVTTL" -to SRAM_D[0]
set_instance_assignment -name IO_STANDARD "3.3-V LVTTL" -to SRAM_D[1]
set_instance_assignment -name IO_STANDARD "3.3-V LVTTL" -to SRAM_D[2]
set_instance_assignment -name IO_STANDARD "3.3-V LVTTL" -to SRAM_D[3]
set_instance_assignment -name IO_STANDARD "3.3-V LVTTL" -to SRAM_D[4]
set_instance_assignment -name IO_STANDARD "3.3-V LVTTL" -to SRAM_D[5]
set_instance_assignment -name IO_STANDARD "3.3-V LVTTL" -to SRAM_D[6]
set_instance_assignment -name IO_STANDARD "3.3-V LVTTL" -to SRAM_D[7]
set_instance_assignment -name IO_STANDARD "3.3-V LVTTL" -to SRAM_D[8]
set_instance_assignment -name IO_STANDARD "3.3-V LVTTL" -to SRAM_D[9]
set_instance_assignment -name IO_STANDARD "3.3-V LVTTL" -to SRAM_D[10]
set_instance_assignment -name IO_STANDARD "3.3-V LVTTL" -to SRAM_D[11]
set_instance_assignment -name IO_STANDARD "3.3-V LVTTL" -to SRAM_D[12]
set_instance_assignment -name IO_STANDARD "3.3-V LVTTL" -to SRAM_D[13]
set_instance_assignment -name IO_STANDARD "3.3-V LVTTL" -to SRAM_D[14]
set_instance_assignment -name IO_STANDARD "3.3-V LVTTL" -to SRAM_D[15]
set_instance_assignment -name IO_STANDARD "3.3-V LVTTL" -to SRAM_LB_n
set_instance_assignment -name IO_STANDARD "3.3-V LVTTL" -to SRAM_OE_n
set_instance_assignment -name IO_STANDARD "3.3-V LVTTL" -to SRAM_UB_n
set_instance_assignment -name IO_STANDARD "3.3-V LVTTL" -to SRAM_WE_n
set_instance_assignment -name IO_STANDARD "1.2 V" -to SW[0]
set_instance_assignment -name IO_STANDARD "1.2 V" -to SW[1]
set_instance_assignment -name IO_STANDARD "1.2 V" -to SW[2]
set_instance_assignment -name IO_STANDARD "1.2 V" -to SW[3]
set_instance_assignment -name IO_STANDARD "1.2 V" -to SW[4]
set_instance_assignment -name IO_STANDARD "1.2 V" -to SW[5]
set_instance_assignment -name IO_STANDARD "1.2 V" -to SW[6]
set_instance_assignment -name IO_STANDARD "1.2 V" -to SW[7]
set_instance_assignment -name IO_STANDARD "1.2 V" -to SW[8]
set_instance_assignment -name IO_STANDARD "1.2 V" -to SW[9]
set_instance_assignment -name IO_STANDARD "2.5 V" -to UART_RX
set_instance_assignment -name IO_STANDARD "2.5 V" -to UART_TX
set_global_assignment -name ENABLE_SIGNALTAP OFF
set_global_assignment -name USE_SIGNALTAP_FILE stp1.stp
set_global_assignment -name ENABLE_LOGIC_ANALYZER_INTERFACE OFF
set_global_assignment -name EDA_SIMULATION_TOOL "QuestaSim (Verilog)"
set_global_assignment -name EDA_TIME_SCALE "1 ps" -section_id eda_simulation
set_global_assignment -name EDA_OUTPUT_DATA_FORMAT "VERILOG HDL" -section_id eda_simulation
set_global_assignment -name EDA_GENERATE_FUNCTIONAL_NETLIST OFF -section_id eda_board_design_timing
set_global_assignment -name EDA_GENERATE_FUNCTIONAL_NETLIST OFF -section_id eda_board_design_symbol
set_global_assignment -name EDA_GENERATE_FUNCTIONAL_NETLIST OFF -section_id eda_board_design_signal_integrity
set_global_assignment -name EDA_GENERATE_FUNCTIONAL_NETLIST OFF -section_id eda_board_design_boundary_scan
set_global_assignment -name VERILOG_INPUT_VERSION SYSTEMVERILOG_2005
set_global_assignment -name VERILOG_SHOW_LMF_MAPPING_MESSAGES OFF
set_global_assignment -name SEARCH_PATH /home/apistol/private/rv32/rtl/cpu
set_global_assignment -name SEARCH_PATH /home/apistol/private/rv32/ip/intel
set_global_assignment -name SEARCH_PATH /home/apistol/private/rv32/board/terasic_cv_gx/ip
set_global_assignment -name OPTIMIZATION_MODE "HIGH PERFORMANCE EFFORT"
set_global_assignment -name ROUTER_CLOCKING_TOPOLOGY_ANALYSIS ON
set_global_assignment -name PHYSICAL_SYNTHESIS_REGISTER_DUPLICATION ON
set_instance_assignment -name AUTO_GLOBAL_CLOCK ON -to CLOCK_125_p
set_instance_assignment -name GLOBAL_SIGNAL GLOBAL_CLOCK -to CLOCK_125_p
set_global_assignment -name QIP_FILE ip/IP_SDRAM.qip
set_global_assignment -name SDC_FILE SoC.sdc
set_global_assignment -name SYSTEMVERILOG_FILE rtl/SDRAM_interface.sv
set_global_assignment -name SYSTEMVERILOG_FILE rtl/SoC.sv
set_global_assignment -name SYSTEMVERILOG_FILE ../../rtl/peripherials/WriteBuffer.sv
set_global_assignment -name SYSTEMVERILOG_FILE ../../rtl/peripherials/VIDEO_controller.sv
set_global_assignment -name SYSTEMVERILOG_FILE ../../rtl/peripherials/VIDEO_VGA.sv
set_global_assignment -name SYSTEMVERILOG_FILE ../../rtl/peripherials/UART_TX.sv
set_global_assignment -name SYSTEMVERILOG_FILE ../../rtl/peripherials/UART_RX.sv
set_global_assignment -name SYSTEMVERILOG_FILE ../../rtl/peripherials/UART.sv
set_global_assignment -name SYSTEMVERILOG_FILE ../../rtl/peripherials/Timer.sv
set_global_assignment -name SYSTEMVERILOG_FILE ../../rtl/peripherials/SRAM_interface.sv
set_global_assignment -name SYSTEMVERILOG_FILE ../../rtl/peripherials/SD.sv
set_global_assignment -name SYSTEMVERILOG_FILE ../../rtl/peripherials/RESET.sv
set_global_assignment -name SYSTEMVERILOG_FILE ../../rtl/peripherials/PLIC.sv
set_global_assignment -name SYSTEMVERILOG_FILE ../../rtl/peripherials/LED.sv
set_global_assignment -name SYSTEMVERILOG_FILE ../../rtl/peripherials/I2C.sv
set_global_assignment -name SYSTEMVERILOG_FILE ../../rtl/peripherials/GPIO.sv
set_global_assignment -name SYSTEMVERILOG_FILE ../../rtl/peripherials/FIFO.sv
set_global_assignment -name SYSTEMVERILOG_FILE ../../rtl/peripherials/DMA.sv
set_global_assignment -name SYSTEMVERILOG_FILE ../../rtl/peripherials/BusAccess.sv
set_global_assignment -name SYSTEMVERILOG_FILE ../../rtl/peripherials/BRIDGE.sv
set_global_assignment -name SYSTEMVERILOG_FILE ../../rtl/peripherials/BROM.sv
set_global_assignment -name SYSTEMVERILOG_FILE ../../rtl/peripherials/BRAM.sv
set_global_assignment -name SYSTEMVERILOG_FILE ../../rtl/peripherials/BRAM_dual.sv
set_global_assignment -name SYSTEMVERILOG_FILE ../../rtl/peripherials/BRAM_latency.sv
set_global_assignment -name SYSTEMVERILOG_FILE ../../rtl/peripherials/BRAM_clear.sv
set_global_assignment -name SYSTEMVERILOG_FILE ../../rtl/peripherials/AUDIO_pwm_output.sv
set_global_assignment -name SYSTEMVERILOG_FILE ../../rtl/peripherials/AUDIO_controller.sv
set_global_assignment -name QIP_FILE ../../ip/intel/IP_UnsignedMultiply.qip
set_global_assignment -name QIP_FILE ../../ip/intel/IP_UnsignedDivide.qip
set_global_assignment -name QIP_FILE ../../ip/intel/IP_Multiply.qip
set_global_assignment -name QIP_FILE ../../ip/intel/IP_Divide.qip
set_global_assignment -name SIP_FILE ip/IP_SDRAM.sip
set_global_assignment -name SYSTEMVERILOG_FILE ../../rtl/cpu/private/CPU_WriteBuffer.sv
set_global_assignment -name SYSTEMVERILOG_FILE ../../rtl/cpu/private/CPU_Writeback.sv
set_global_assignment -name SYSTEMVERILOG_FILE ../../rtl/cpu/private/CPU_Types.sv
set_global_assignment -name SYSTEMVERILOG_FILE ../../rtl/cpu/private/CPU_SkidBuffer.sv
set_global_assignment -name SYSTEMVERILOG_FILE ../../rtl/cpu/private/CPU_Registers.sv
set_global_assignment -name SYSTEMVERILOG_FILE ../../rtl/cpu/private/CPU_PreDecode.sv
set_global_assignment -name SYSTEMVERILOG_FILE ../../rtl/cpu/private/CPU_Multiply.sv
set_global_assignment -name SYSTEMVERILOG_FILE ../../rtl/cpu/private/CPU_Memory.sv
set_global_assignment -name SYSTEMVERILOG_FILE ../../rtl/cpu/private/CPU_ICache_Comb.sv
set_global_assignment -name SYSTEMVERILOG_FILE ../../rtl/cpu/private/CPU_Forward.sv
set_global_assignment -name SYSTEMVERILOG_FILE ../../rtl/cpu/private/CPU_Fetch.sv
set_global_assignment -name SYSTEMVERILOG_FILE ../../rtl/cpu/private/CPU_Execute.sv
set_global_assignment -name SYSTEMVERILOG_FILE ../../rtl/cpu/private/CPU_Divide.sv
set_global_assignment -name SYSTEMVERILOG_FILE ../../rtl/cpu/private/CPU_Defines.sv
set_global_assignment -name SYSTEMVERILOG_FILE ../../rtl/cpu/private/CPU_Decode.sv
set_global_assignment -name SYSTEMVERILOG_FILE ../../rtl/cpu/private/CPU_DCache_Reg.sv
set_global_assignment -name SYSTEMVERILOG_FILE ../../rtl/cpu/private/CPU_DCache_None.sv
set_global_assignment -name SYSTEMVERILOG_FILE ../../rtl/cpu/private/CPU_DCache_Comb.sv
set_global_assignment -name SYSTEMVERILOG_FILE ../../rtl/cpu/private/CPU_CSR.sv
set_global_assignment -name SYSTEMVERILOG_FILE ../../rtl/cpu/private/CPU_ALU.sv
set_global_assignment -name SYSTEMVERILOG_FILE ../../rtl/cpu/CPU.sv
set_global_assignment -name QIP_FILE ip/IP_PLL_Clk.qip
set_global_assignment -name SIP_FILE ip/IP_PLL_Clk.sip
set_global_assignment -name SIGNALTAP_FILE SoC.stp
set_location_assignment PIN_T21 -to uart_1_rx
set_location_assignment PIN_D26 -to uart_1_tx
set_instance_assignment -name IO_STANDARD "3.3-V LVTTL" -to uart_1_rx
set_instance_assignment -name IO_STANDARD "3.3-V LVTTL" -to uart_1_tx
set_instance_assignment -name PARTITION_HIERARCHY root_partition -to | -section_id Top
