apistol78/rv32/rtl/peripherials/SDRAM_controller.sv

/*
 TRAKTOR
 Copyright (c) 2023 Anders Pistol.

 This Source Code Form is subject to the terms of the Mozilla Public
 License, v. 2.0. If a copy of the MPL was not distributed with this
 file, You can obtain one at https://mozilla.org/MPL/2.0/.
*/
/*

Memory mapping

 2 bank bits
13 row bits
 9 column bits
--------------
24 bits total

2222 1111 1111 1100 0000 0000
3210 9876 5432 1098 7654 3210
.RRR RRRR RRRR RRBB CCCC CCCC 0

*/

module SDRAM_controller #(
	parameter FREQUENCY = 100_000_000,

	// User
	parameter USER_DATA_WIDTH = 32,

	// SDRAM chip
	parameter SDRAM_ADDRESS_WIDTH = 13,
	parameter SDRAM_DATA_WIDTH = 16
)(
	input i_reset,
	input i_clock,
	input i_clock_sdram,			// Offset from i_clock to help with timing.

	input i_request,
	input i_rw,
	input [31:0] i_address,			// Must be 4 byte aligned.
	input [USER_DATA_WIDTH-1:0] i_wdata,
	output logic [USER_DATA_WIDTH-1:0] o_rdata,
	output bit o_ready,

	output bit sdram_clk,
	output bit sdram_clk_en,
	output bit sdram_cas_n,
	output bit sdram_cs_n,
	output bit sdram_ras_n,
	output bit sdram_we_n,
	output bit [1:0] sdram_dqm,
	output bit [1:0] sdram_bs,		// Also commonly called BA.
	output bit [SDRAM_ADDRESS_WIDTH-1:0] sdram_addr,
	
	input [SDRAM_DATA_WIDTH-1:0] sdram_rdata,
	output bit [SDRAM_DATA_WIDTH-1:0] sdram_wdata,
	output bit sdram_data_rw
);
	// Calculate burst length.
	localparam BURST_COUNT = USER_DATA_WIDTH / SDRAM_DATA_WIDTH;

	// Bit spans.
	localparam Ba = 0;
	localparam Bb = SDRAM_DATA_WIDTH;
	localparam Bc = SDRAM_DATA_WIDTH * 2;
	localparam Bd = SDRAM_DATA_WIDTH * 3;
	localparam Be = SDRAM_DATA_WIDTH * 4;
	localparam Bf = SDRAM_DATA_WIDTH * 5;
	localparam Bg = SDRAM_DATA_WIDTH * 6;
	localparam Bh = SDRAM_DATA_WIDTH * 7;
	localparam Bi = SDRAM_DATA_WIDTH * 8;

	// Timing parameters.
	localparam STARTUP_COUNT	= 20000;			// startup delay, 100 us
	localparam tRP_COUNT		= 1;				// wait precharge, 20 ns
	localparam tRFC_COUNT		= 7; 				// wait refresh, 65 ns
	localparam tMRD_COUNT		= 2000;				// wait set mode, 2000 cyc @ 100 MHz
	localparam tRCD_COUNT		= 3 + BURST_COUNT;	// wait read/write, 65 ns
	localparam tACT_COUNT		= 1;				// wait activate
	
	// Types
	typedef enum bit [3:0]
	{
		CMD_NOP	= 4'b0111,
		CMD_PRECHARGE = 4'b0010,
		CMD_SET_MODE = 4'b0000,
		CMD_REFRESH = 4'b0001,
		CMD_ACTIVATE = 4'b0011,
		CMD_READ = 4'b0101,
		CMD_WRITE = 4'b0100
	} command_t;

	typedef enum bit [5:0]
	{
		STATE_STARTUP,
		STATE_STARTUP_PRECHARGE,
		STATE_STARTUP_WAIT_PRECHARGE,
		STATE_STARTUP_AUTO_REFRESH_1,
		STATE_STARTUP_AUTO_REFRESH_2,
		STATE_STARTUP_WAIT_AUTO_REFRESH,
		STATE_STARTUP_SET_MODE,
		STATE_STARTUP_WAIT_SET_MODE,
		STATE_IDLE,
		STATE_REFRESH,
		STATE_WAIT_REFRESH,
		STATE_WAIT_ACTIVATE,
		STATE_WAIT_ACTIVATE_END,
		STATE_WAIT_READ,
		STATE_WAIT_WRITE,
		STATE_WAIT_PRECHARGE,
		STATE_WAIT_PRECHARGE_ALL,
		STATE_END_REQUEST
	} state_t;

	typedef enum bit [0:0]
	{
		WBM_PROGRAMMED_BURST_LENGTH = 1'b0,	// Burst read and burst write
		WBM_SINGLE_LOCATION_ACCESS = 1'b1	// Burst read and single write
	}
	write_burst_mode_t;

	typedef enum bit [2:0]
	{
		CAS_2 = 3'b010,
		CAS_3 = 3'b011
	}
	cas_t;

	typedef enum bit [2:0]
	{
		BURST_1 = 3'b000,
		BURST_2 = 3'b001,
		BURST_4 = 3'b010,
		BURST_8 = 3'b011,
		BURST_PAGE = 3'b111
	}
	burst_length_t;

	state_t state = STATE_STARTUP;
	bit [15:0] count = STARTUP_COUNT;
	bit [31:0] refresh = 0;
	bit should_refresh = 1'b0;
	command_t command = CMD_NOP;
	bit [USER_DATA_WIDTH-1:0] wdata;
	bit [22:0] address;
	bit [13:0] active_rows [3:0];	// Active row in each bank.

	// Initial
	initial begin
		o_ready = 1'b0;

		// Ensure DQM and CKE are high during initial.
		sdram_dqm = 2'b11;
		sdram_clk_en = 1'b0;

		// Others
		sdram_bs = 2'b00;
		sdram_addr = 13'b0;
		sdram_wdata = 0;

		active_rows[0] = { 1'b1, 13'b0 };
		active_rows[1] = { 1'b1, 13'b0 };
		active_rows[2] = { 1'b1, 13'b0 };
		active_rows[3] = { 1'b1, 13'b0 };
	end

	// Combinatorial
	assign sdram_clk = i_clock_sdram;
	assign sdram_cs_n = command[3];
	assign sdram_ras_n = command[2];
	assign sdram_cas_n = command[1];
	assign sdram_we_n = command[0];

	//=============================================

	wire [22:0] i_address_dw = i_address[24:2];
	wire [1:0] i_address_dw_bank = i_address_dw[9:8];
	wire [12:0] i_address_dw_row = i_address_dw[22:10];

	//=============================================

    logic [SDRAM_DATA_WIDTH-1:0] r_ram_data = 0;
    logic [SDRAM_DATA_WIDTH-1:0] r_ram_data_ext_clk = 0;
    always_ff @(posedge i_clock) begin
        { r_ram_data, r_ram_data_ext_clk } <= { r_ram_data_ext_clk, sdram_rdata };
    end	

	//=============================================
	
	always_comb begin
		sdram_data_rw = i_rw;
	end
	
	always_ff @(posedge i_clock) begin
		if (i_reset) begin
			state <= STATE_STARTUP;
			count <= STARTUP_COUNT;
			refresh <= 0;
			should_refresh <= 1'b0;
			command <= CMD_NOP;

			active_rows[0] <= { 1'b1, 13'b0 };
			active_rows[1] <= { 1'b1, 13'b0 };
			active_rows[2] <= { 1'b1, 13'b0 };
			active_rows[3] <= { 1'b1, 13'b0 };
		end
		else begin

			// Decrement startup counter.
			count <= count - 1;

			// Check if we should refresh.
			refresh <= refresh + 1;
			if (refresh >= 32'd50_0) begin
				refresh <= 0;
				should_refresh <= 1'b1;
			end

			case (state)
			
				/*
				Startup stage, output NOP.
				Enable clock after some time.
				*/
				STATE_STARTUP: begin
					command <= CMD_NOP;
					
					// Enable clock after 25% of startup time has passed.
					if (count <= (STARTUP_COUNT * 3) / 4) begin
						sdram_dqm <= 2'b00;
						sdram_clk_en <= 1'b1;
					end

					if (count == 0) begin
						state <= STATE_STARTUP_PRECHARGE;
					end
				end

				/*
				Precharge all banks.
				*/
				STATE_STARTUP_PRECHARGE: begin
					command <= CMD_PRECHARGE;

					sdram_bs <= 2'b00;
					sdram_addr <= { 2'b00, 1'b1, 10'b0000000000 };	// A10 set to precharge all banks.

					count <= tRP_COUNT;
					state <= STATE_STARTUP_WAIT_PRECHARGE;
				end
				
				/*
				Wait until startup precharge has finished.
				*/
				STATE_STARTUP_WAIT_PRECHARGE: begin
					command <= CMD_NOP;
					if (count == 0) begin
						state <= STATE_STARTUP_AUTO_REFRESH_1;
					end				
				end
				
				/*
				Perform startup auto refresh.
				*/
				STATE_STARTUP_AUTO_REFRESH_1: begin
					command <= CMD_REFRESH;
					state <= STATE_STARTUP_AUTO_REFRESH_2;
				end

				/*
				Perform startup auto refresh.
				*/
				STATE_STARTUP_AUTO_REFRESH_2: begin
					command <= CMD_REFRESH;
					count <= tRFC_COUNT;
					state <= STATE_STARTUP_WAIT_AUTO_REFRESH;
				end

				/*
				Wait until startup auto refresh finished.
				*/
				STATE_STARTUP_WAIT_AUTO_REFRESH: begin
					command <= CMD_NOP;
					if (count == 0) begin
						state <= STATE_STARTUP_SET_MODE;
					end	
				end	

				/*
				Set DRAM mode.
				*/
				STATE_STARTUP_SET_MODE: begin
					command <= CMD_SET_MODE;
					sdram_bs <= 2'b00;

					if (BURST_COUNT == 1)
						sdram_addr <= { 3'b000, WBM_PROGRAMMED_BURST_LENGTH, 2'b00, CAS_2, 1'b0, BURST_1 };	// ?,Write Burst Mode,?,CAS,Burst Type,Burst Length
					else if (BURST_COUNT == 2)
						sdram_addr <= { 3'b000, WBM_PROGRAMMED_BURST_LENGTH, 2'b00, CAS_2, 1'b0, BURST_2 };
					else if (BURST_COUNT == 4)
						sdram_addr <= { 3'b000, WBM_PROGRAMMED_BURST_LENGTH, 2'b00, CAS_2, 1'b0, BURST_4 };
					else if (BURST_COUNT == 8)
						sdram_addr <= { 3'b000, WBM_PROGRAMMED_BURST_LENGTH, 2'b00, CAS_2, 1'b0, BURST_8 };

					count <= tMRD_COUNT;
					state <= STATE_STARTUP_WAIT_SET_MODE;
				end
				
				/*
				Wait until mode has been set.
				*/
				STATE_STARTUP_WAIT_SET_MODE: begin
					command <= CMD_NOP;
					if (count == 0) begin
						state <= STATE_IDLE;
					end	
				end

				//=================================================

				/*
				Idle state, wait for requests. Dispatch refresh
				cycles.
				*/
				STATE_IDLE: begin
					command <= CMD_NOP;

					o_ready <= 1'b0;

					if (should_refresh) begin
						should_refresh <= 1'b0;

						if (
							active_rows[0][13] == 1'b0 ||
							active_rows[1][13] == 1'b0 ||
							active_rows[2][13] == 1'b0 ||
							active_rows[3][13] == 1'b0
						)
						begin
							// Close all active rows, cannot be opened during refresh.
							active_rows[0] <= { 1'b1, 13'b0 };
							active_rows[1] <= { 1'b1, 13'b0 };
							active_rows[2] <= { 1'b1, 13'b0 };
							active_rows[3] <= { 1'b1, 13'b0 };

							command <= CMD_PRECHARGE;

							sdram_bs <= 2'b00;
							sdram_addr <= { 4'b0000, 8'b0000_0000, 1'b0 };
							sdram_addr[10] <= 1'b1;

							count <= tRP_COUNT;
							state <= STATE_WAIT_PRECHARGE_ALL;
						end
						else begin
							// No active rows, just refresh.
							state <= STATE_REFRESH;
						end

					end
					else if (i_request) begin
						$display("---- request begin (bank %d) ----", i_address_dw_bank);

						address <= i_address_dw;
						wdata <= i_wdata;

						if (active_rows[i_address_dw_bank] == { 1'b0, i_address_dw_row }) begin
							// Row already active, do RW immediately.
							$display("ROW already active (%x)", i_address);
							count <= 0;
							state <= STATE_WAIT_ACTIVATE;
						end
						else if (active_rows[i_address_dw_bank][13] == 1'b1) begin
							// No bank active, activate before RW.
							$display("No ROW active, activate (%x)", i_address);
							active_rows[i_address_dw_bank] <= { 1'b0, i_address_dw_row };

							command <= CMD_ACTIVATE;

							sdram_bs <= i_address_dw_bank;
							sdram_addr <= i_address_dw_row;

							count <= tACT_COUNT;
							state <= STATE_WAIT_ACTIVATE;			

						end
						else begin
							// Other bank active, precharge old and activate new before RW.
							$display("Other ROW active, close old and activate (%x)", i_address);
							active_rows[i_address_dw_bank] <= { 1'b0, i_address_dw_row };

							command <= CMD_PRECHARGE;

							sdram_bs <= i_address_dw_bank;
							sdram_addr <= active_rows[i_address_dw_bank][12:0];
							sdram_addr[10] <= 1'b0;

							count <= tRP_COUNT;
							state <= STATE_WAIT_PRECHARGE;
						end
					end
				end

				/*
				Issue refresh command.
				*/
				STATE_REFRESH: begin
					command <= CMD_REFRESH;
					count <= tRFC_COUNT;
					state <= STATE_WAIT_REFRESH;
				end

				/*
				Wait until refresh has finished.
				*/
				STATE_WAIT_REFRESH: begin
					command <= CMD_NOP;
					if (count == 0) begin
						state <= STATE_IDLE;
					end
				end

				/*
				Wait until activation of row finish,
				then dispatch read or write states.
				*/
				STATE_WAIT_ACTIVATE: begin
					command <= CMD_NOP;
					if (count == 0) begin
						sdram_bs <= address[9:8];
						sdram_addr <= { 4'b0000, address[7:0], 1'b0 };
						sdram_addr[10] <= 1'b0;
						
						if (BURST_COUNT == 1)
							sdram_wdata <= wdata;
						else if (BURST_COUNT == 2)
							sdram_wdata <= wdata[Bc-1:Bb];
						else if (BURST_COUNT == 4)
							sdram_wdata <= wdata[Be-1:Bd];
						else if (BURST_COUNT == 8)
							sdram_wdata <= wdata[Bi-1:Bh];

						state <= STATE_WAIT_ACTIVATE_END;
					end
				end

				STATE_WAIT_ACTIVATE_END: begin
					command <= i_rw ? CMD_WRITE : CMD_READ;
					count <= tRCD_COUNT;
					state <= i_rw ? STATE_WAIT_WRITE : STATE_WAIT_READ;
				end

				/*
				Wait until read command finishes, latch data.
				*/
				STATE_WAIT_READ: begin
					command <= CMD_NOP;

					if (BURST_COUNT == 1) begin
						if (count == tRCD_COUNT - 4) begin
							o_rdata <= r_ram_data;
						end
					end
					else if (BURST_COUNT == 2) begin
						if (count == tRCD_COUNT - 4) begin
							o_rdata[Bc-1:Bb] <= r_ram_data;
						end
						else if (count == tRCD_COUNT - 5) begin
							o_rdata[Bb-1:Ba] <= r_ram_data;
						end						
					end
					else if (BURST_COUNT == 4) begin
						if (count == tRCD_COUNT - 4) begin
							o_rdata[Be-1:Bd] <= r_ram_data;
						end
						else if (count == tRCD_COUNT - 5) begin
							o_rdata[Bd-1:Bc] <= r_ram_data;
						end
						else if (count == tRCD_COUNT - 6) begin
							o_rdata[Bc-1:Bb] <= r_ram_data;
						end
						else if (count == tRCD_COUNT - 7) begin
							o_rdata[Bb-1:Ba] <= r_ram_data;
						end						
					end
					else if (BURST_COUNT == 8) begin
						if (count == tRCD_COUNT - 4) begin
							o_rdata[Bi-1:Bh] <= r_ram_data;
						end
						else if (count == tRCD_COUNT - 5) begin
							o_rdata[Bh-1:Bg] <= r_ram_data;
						end
						else if (count == tRCD_COUNT - 6) begin
							o_rdata[Bg-1:Bf] <= r_ram_data;
						end
						else if (count == tRCD_COUNT - 7) begin
							o_rdata[Bf-1:Be] <= r_ram_data;
						end
						else if (count == tRCD_COUNT - 8) begin
							o_rdata[Be-1:Bd] <= r_ram_data;
						end
						else if (count == tRCD_COUNT - 9) begin
							o_rdata[Bd-1:Bc] <= r_ram_data;
						end
						else if (count == tRCD_COUNT - 10) begin
							o_rdata[Bc-1:Bb] <= r_ram_data;
						end
						else if (count == tRCD_COUNT - 11) begin
							o_rdata[Bb-1:Ba] <= r_ram_data;
						end
					end

					if (count == 0) begin
						o_ready <= 1'b1;
						state <= STATE_END_REQUEST;
					end
				end

				/*
				Wait until write command finishes.
				*/
				STATE_WAIT_WRITE: begin
					command <= CMD_NOP;

					if (BURST_COUNT == 2) begin
						sdram_wdata <= wdata[Bb-1:Ba];
					end
					else if (BURST_COUNT == 4) begin
						if (count == tRCD_COUNT) begin
							sdram_wdata <= wdata[Bd-1:Bc];
						end
						else if (count == tRCD_COUNT - 1) begin
							sdram_wdata <= wdata[Bc-1:Bb];
						end
						else if (count == tRCD_COUNT - 2) begin
							sdram_wdata <= wdata[Bb-1:Ba];
						end
					end
					else if (BURST_COUNT == 8) begin
						if (count == tRCD_COUNT) begin
							sdram_wdata <= wdata[Bh-1:Bg];
						end
						else if (count == tRCD_COUNT - 1) begin
							sdram_wdata <= wdata[Bg-1:Bf];
						end
						else if (count == tRCD_COUNT - 2) begin
							sdram_wdata <= wdata[Bf-1:Be];
						end
						else if (count == tRCD_COUNT - 3) begin
							sdram_wdata <= wdata[Be-1:Bd];
						end
						else if (count == tRCD_COUNT - 4) begin
							sdram_wdata <= wdata[Bd-1:Bc];
						end
						else if (count == tRCD_COUNT - 5) begin
							sdram_wdata <= wdata[Bc-1:Bb];
						end
						else if (count == tRCD_COUNT - 6) begin
							sdram_wdata <= wdata[Bb-1:Ba];
						end
					end

					if (count == 0) begin
						o_ready <= 1'b1;
						state <= STATE_END_REQUEST;
					end			
				end

				/*
				Wait until precharge finishes.
				*/
				STATE_WAIT_PRECHARGE: begin
					command <= CMD_NOP;
					if (count == 0) begin
						command <= CMD_ACTIVATE;

						sdram_bs <= address[9:8];
						sdram_addr <= address[22:10];

						count <= tACT_COUNT;
						state <= STATE_WAIT_ACTIVATE;			
					end
				end

				/*
				Wait until precharge all finishes.
				*/
				STATE_WAIT_PRECHARGE_ALL: begin
					command <= CMD_NOP;
					if (count == 0) begin
						state <= STATE_REFRESH;
					end
				end

				/*
				*/
				STATE_END_REQUEST: begin
					command <= CMD_NOP;
					if (!i_request) begin
						o_ready <= 1'b0;
						state <= STATE_IDLE;
					end
				end

				/*
				*/
				default: begin
					state <= STATE_STARTUP;
				end
			endcase
		end
	end

endmodule
