apistol78/rv32/rtl/peripherials/VIDEO_controller.sv

/*
 TRAKTOR
 Copyright (c) 2023 Anders Pistol.

 This Source Code Form is subject to the terms of the Mozilla Public
 License, v. 2.0. If a copy of the MPL was not distributed with this
 file, You can obtain one at https://mozilla.org/MPL/2.0/.
*/

`timescale 1ns/1ns

module VIDEO_controller #(
	parameter MAX_PITCH = 640
)(
	input i_clock,

	// CPU
	input i_cpu_request,
	input i_cpu_rw,
	input [31:0] i_cpu_address,
	input [31:0] i_cpu_wdata,
	output bit [31:0] o_cpu_rdata,
	output bit o_cpu_ready,

	// Video
	input i_video_hblank,
	input i_video_vblank,
	input [10:0] i_video_pos_x,
	input [10:0] i_video_pos_y,
	output bit [31:0] o_video_rdata,

	// Memory
	output bit o_vram_pa_request,
	output bit o_vram_pa_rw,
	output bit [31:0] o_vram_pa_address,
	output bit [31:0] o_vram_pa_wdata,
	input [31:0] i_vram_pa_rdata,
	input i_vram_pa_ready,

	output bit o_vram_pb_request,
	output bit o_vram_pb_rw,
	output bit [31:0] o_vram_pb_address,
	output bit [31:0] o_vram_pb_wdata,
	input [31:0] i_vram_pb_rdata,
	input i_vram_pb_ready
);

	bit [31:0] vram_read_offset = 0;
	bit [31:0] vram_pitch = 0;
	bit [1:0] vram_skip = 0;
	bit [31:0] frame_counter = 0;

	//===============================

	initial begin
		o_cpu_ready = 1'b0;
		o_video_rdata = 1'b0;

		o_vram_pa_request = 1'b0;
		o_vram_pa_rw = 1'b0;
		o_vram_pa_address = 32'h0;
		o_vram_pa_wdata = 32'h0;

		o_vram_pb_request = 1'b0;
		o_vram_pb_rw = 1'b0;
		o_vram_pb_address = 32'h0;
		o_vram_pb_wdata = 32'h0;
	end

	//===============================
	// Palette

	bit palette_cpu_request = 0;
	bit [7:0] palette_cpu_address = 0;
	bit [23:0] palette_cpu_wdata = 0;
	bit [7:0] palette_video_address;
	wire [23:0] palette_video_rdata;
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
